mogloce622/Soldering-hot-plate/pictures/1.jpg

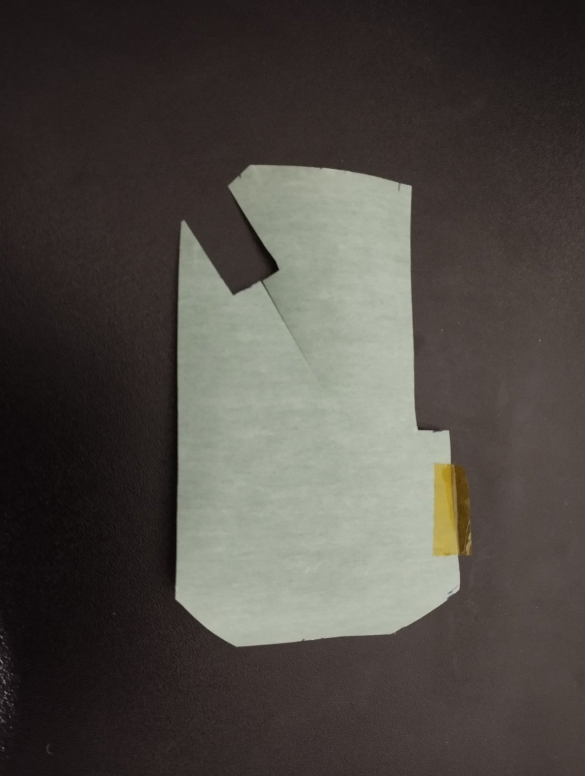
pictures/1.jpg
