mogloce622/Soldering-hot-plate/pictures/2.png

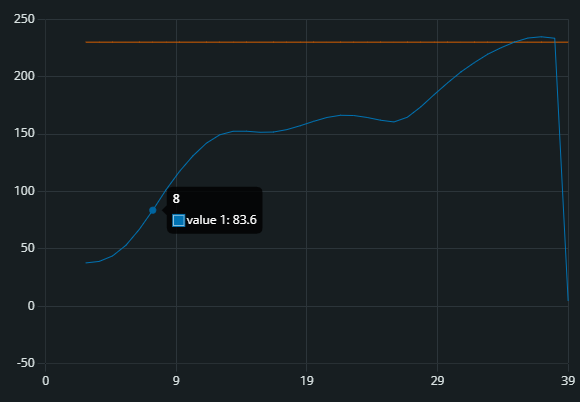
pictures/2.png
