mogloce622/Soldering-hot-plate/pictures/3.jpg

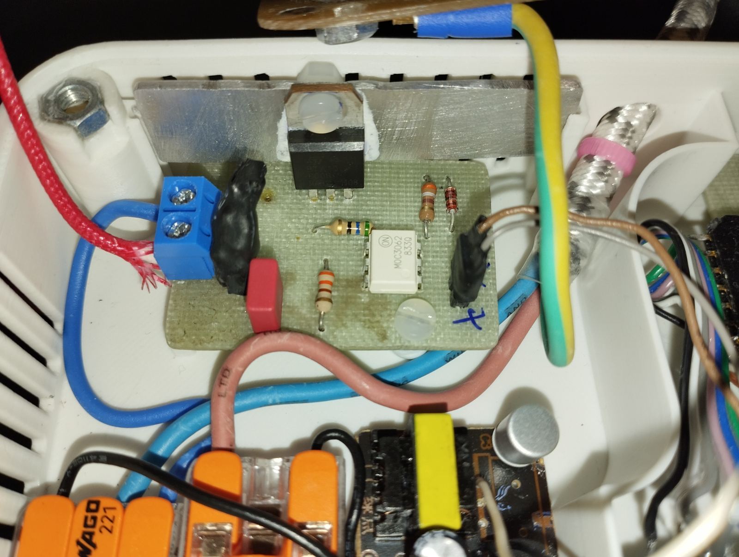
pictures/3.jpg
