mogloce622/Soldering-hot-plate/pictures/4.jpg

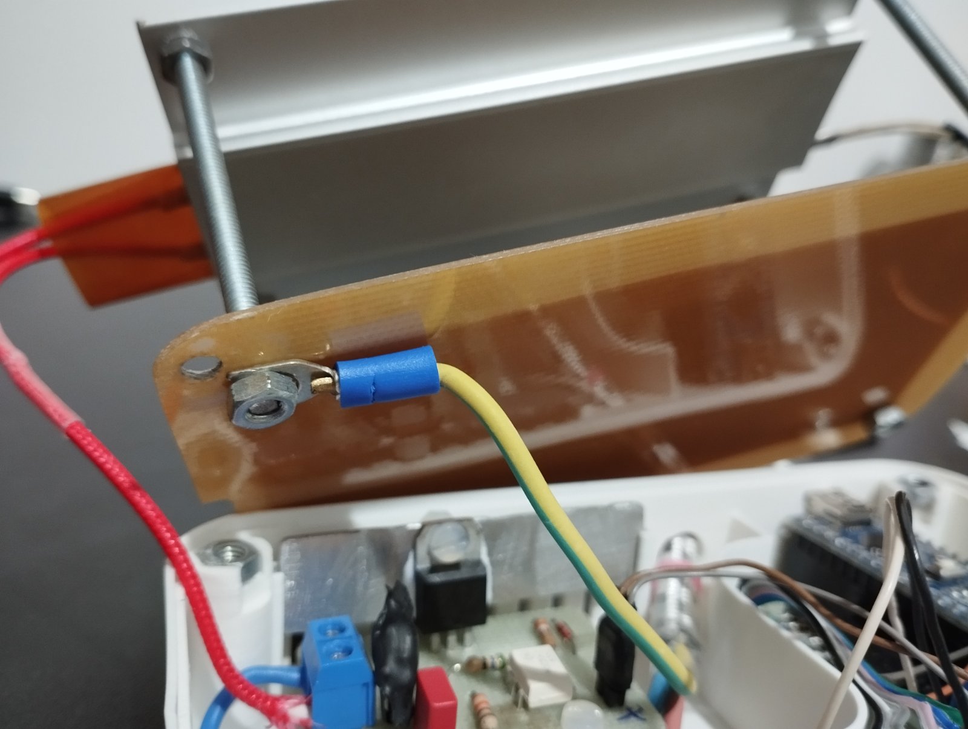
pictures/4.jpg
