mogloce622/Soldering-hot-plate/pictures/5.jpg

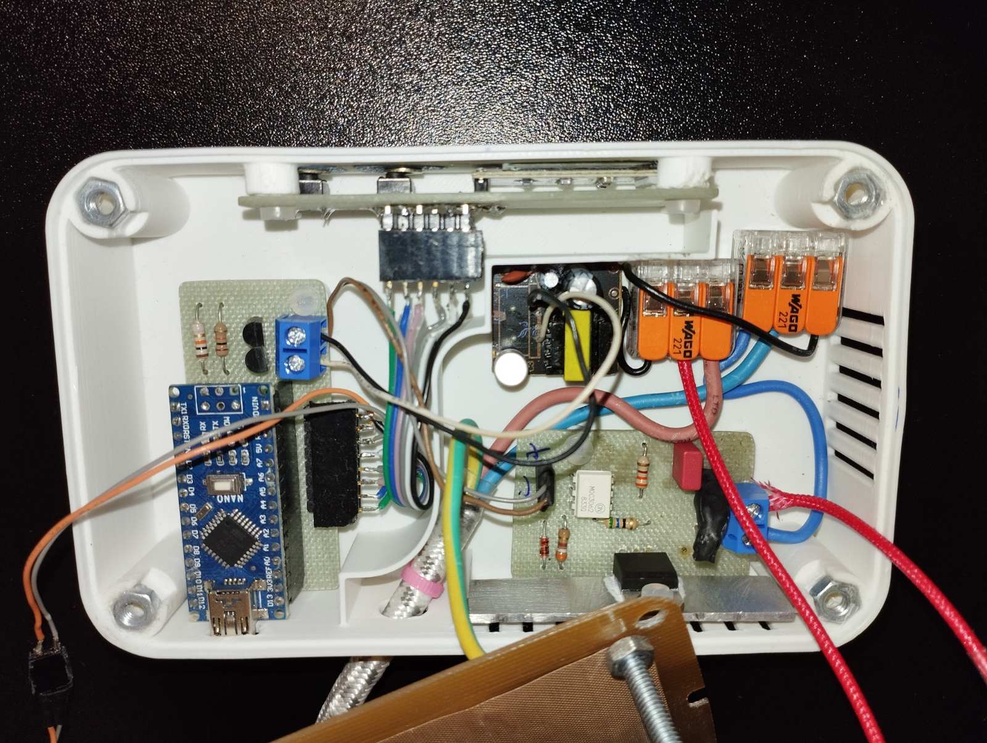
pictures/5.jpg
