mogloce622/Soldering-hot-plate/pictures/7.jpg

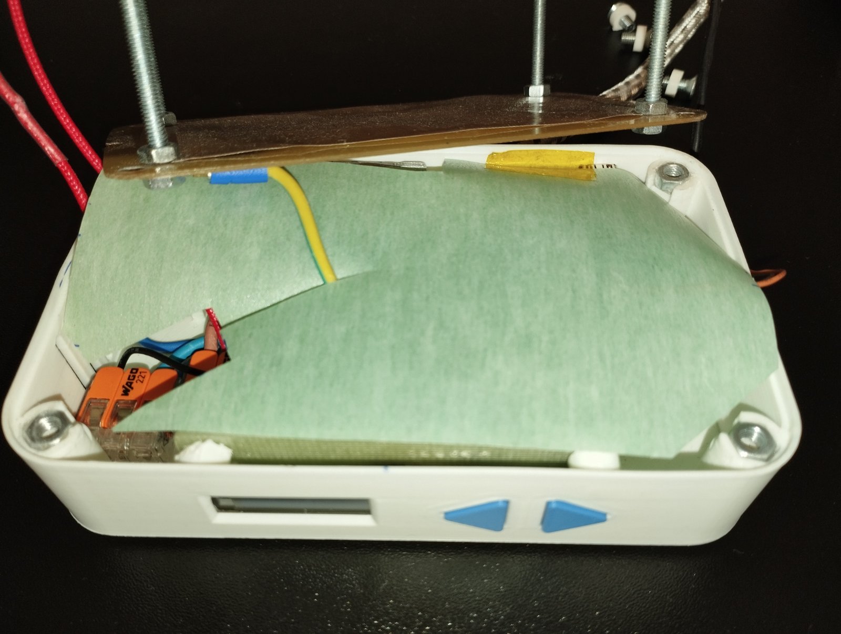
pictures/7.jpg
