mogloce622/Soldering-hot-plate/pictures/8.jpg

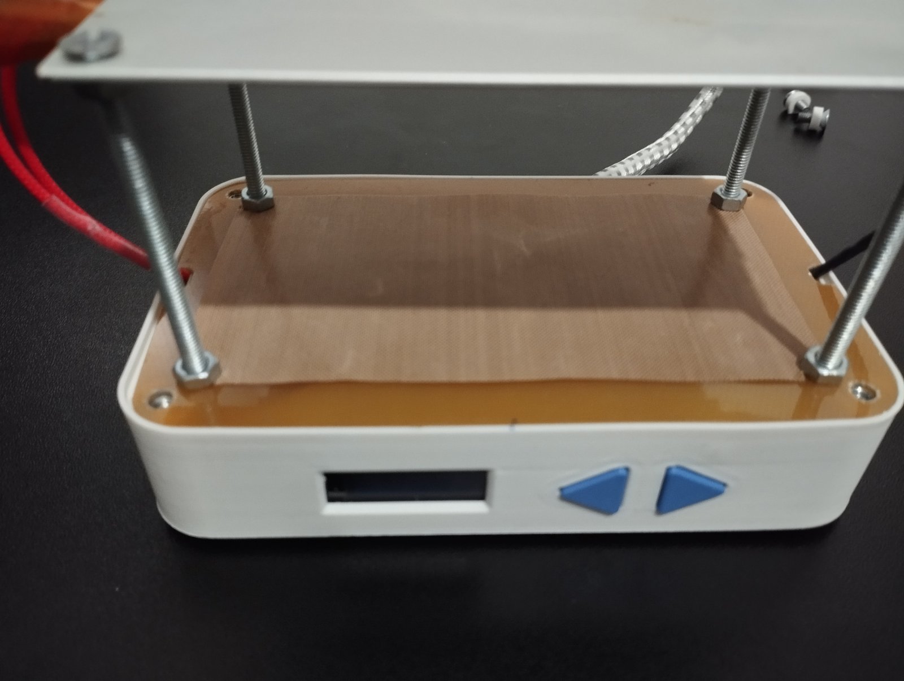
pictures/8.jpg
