mogloce622/Soldering-hot-plate/pictures/9.jpg

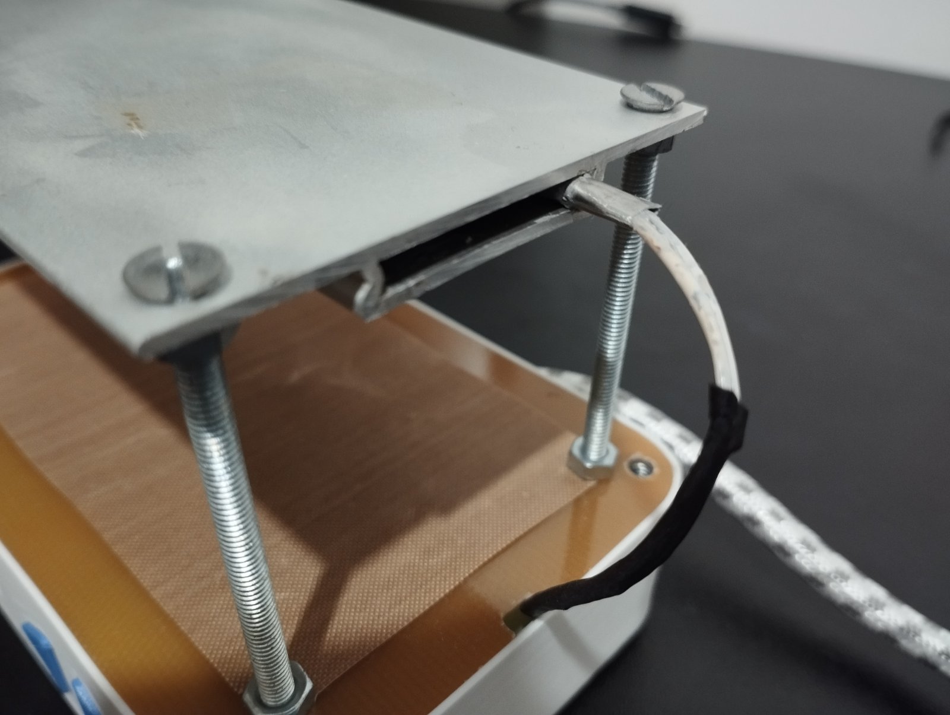
pictures/9.jpg
