mogloce622/Soldering-hot-plate/pictures/10.jpg

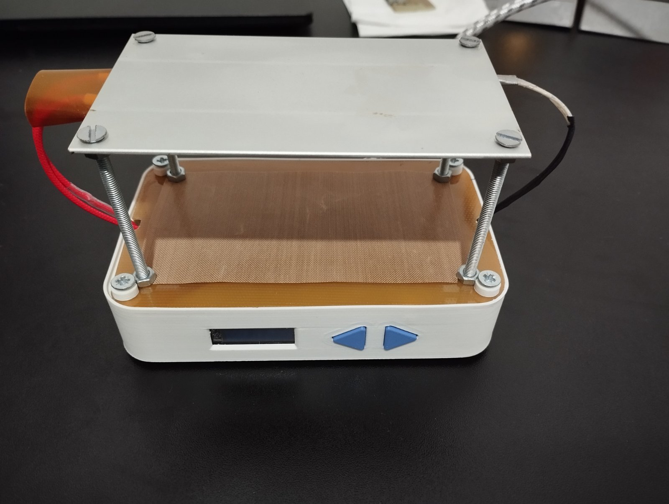
pictures/10.jpg
