mogloce622/Soldering-hot-plate/pictures/11.jpg

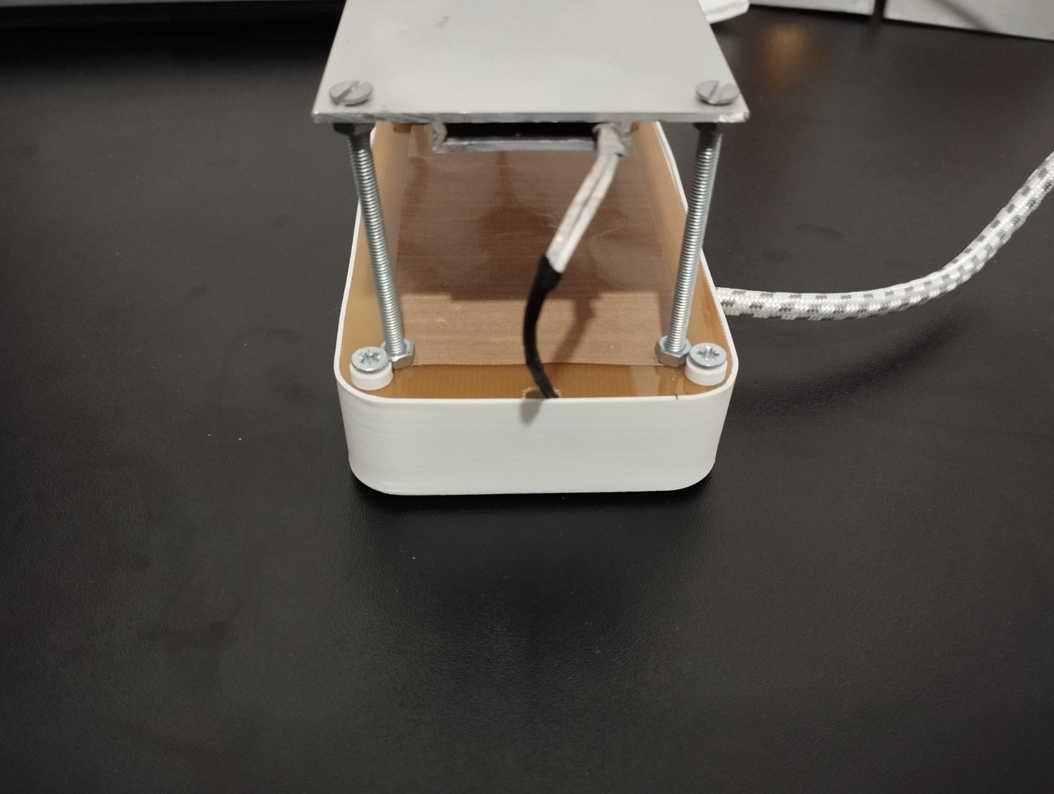
pictures/11.jpg
