mogloce622/Soldering-hot-plate/pictures/12.jpg

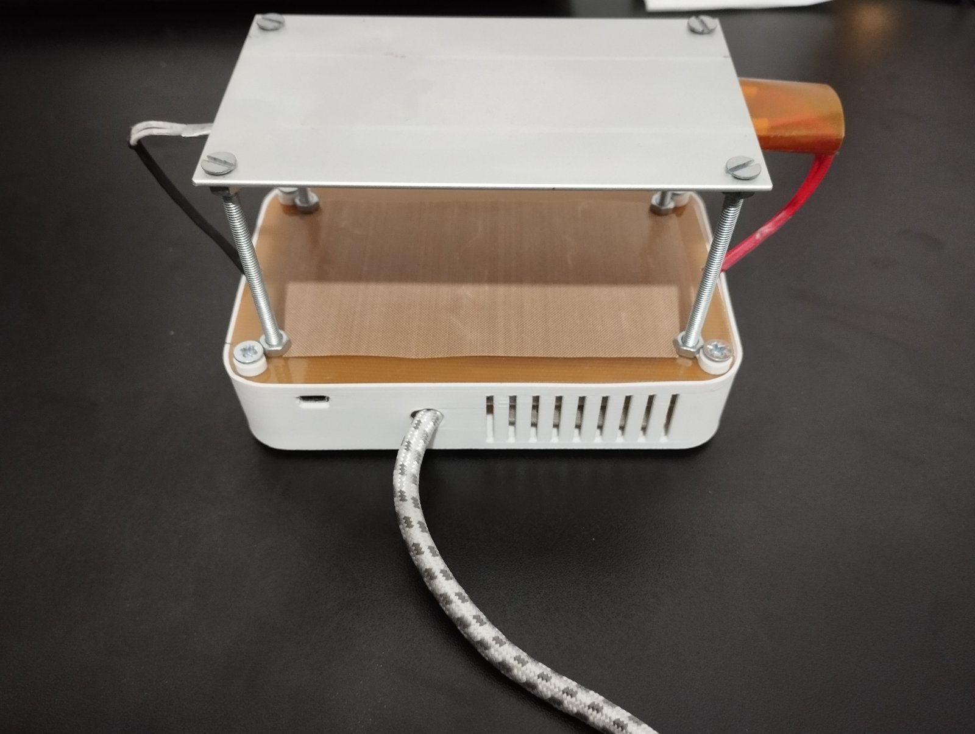
pictures/12.jpg
