mogloce622/Soldering-hot-plate/pictures/13.jpg

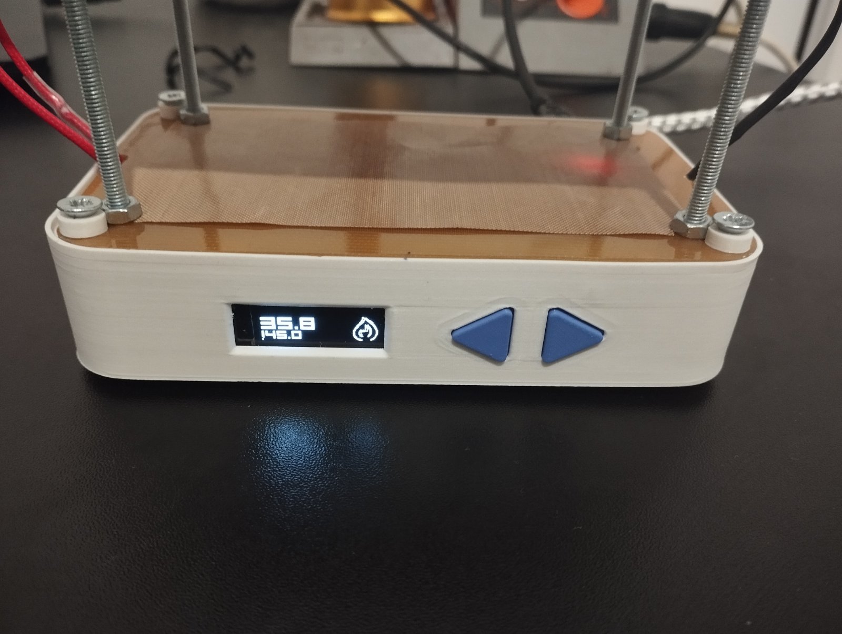
pictures/13.jpg
