mogloce622/Soldering-hot-plate/pictures/15.jpg

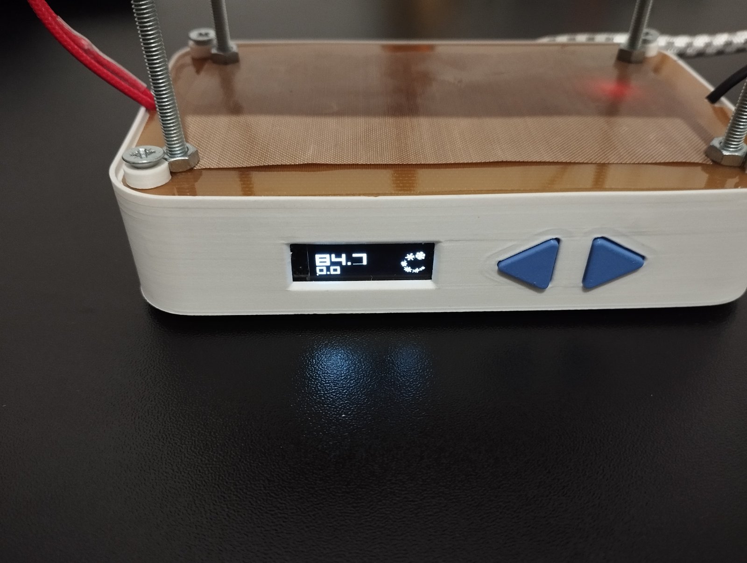
pictures/15.jpg
